michaudtime/lumary-zigbee/docs/research/stock-board-cn1-harness.jpg

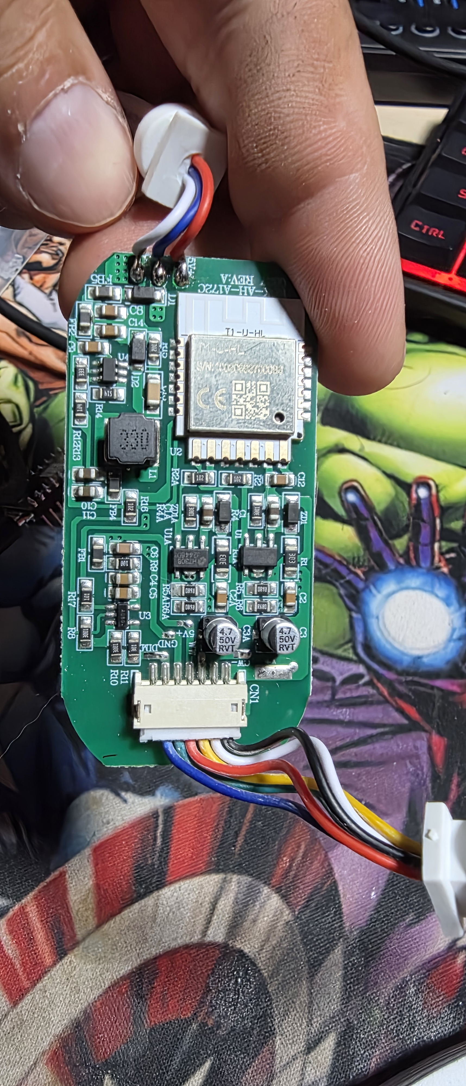
docs/research/stock-board-cn1-harness.jpg
