michaudtime/lumary-zigbee/docs/research/stock-board-cn1-labels.jpg

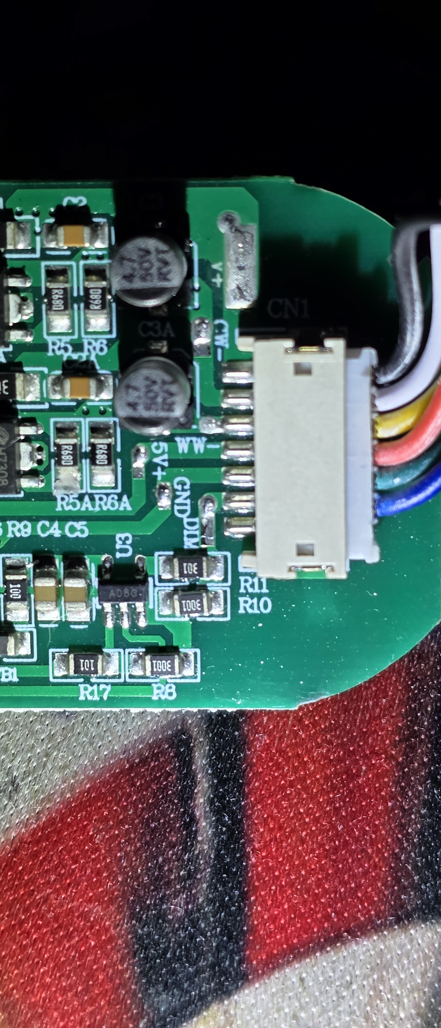
docs/research/stock-board-cn1-labels.jpg
