michaudtime/lumary-zigbee/docs/research/stock-board-top.jpg

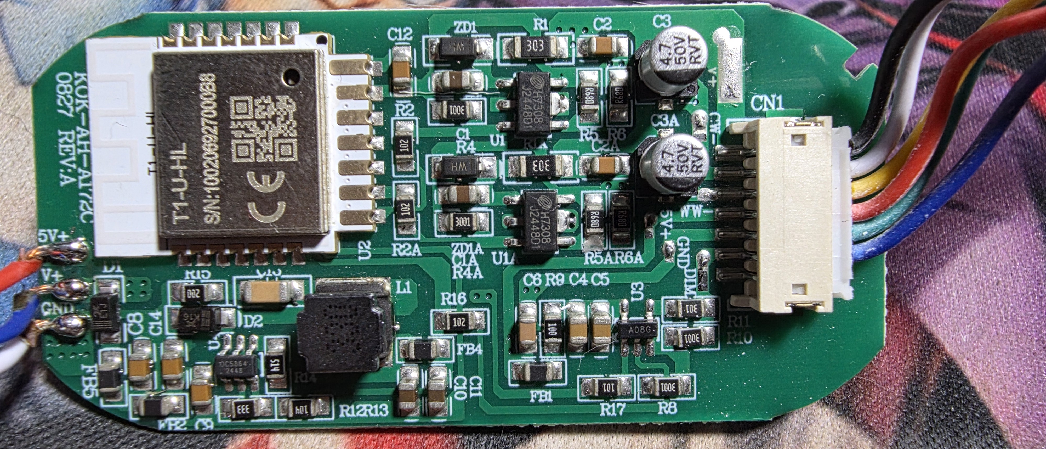
docs/research/stock-board-top.jpg
