michaudtime/lumary-zigbee/hardware/kicad/board-rounded.png

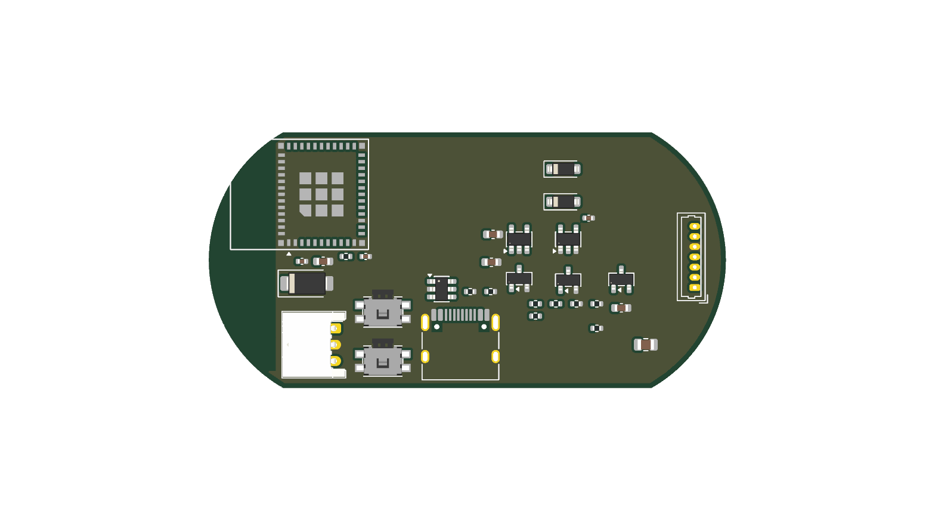
hardware/kicad/board-rounded.png
