michaudtime/lumary-zigbee/src/zigbee_light.cpp

#include "zigbee_light.h"
#include "config.h"
#include "scene_store.h"
#include "effect_params.h"
#include "identify.h"
#include "ring_command.h"
#include <Arduino.h>
#include <string.h>
#include "Zigbee.h"
#include "esp_attr.h"
#include "esp_system.h"
#include "ota_watch.h"
#include "ota_snapshot.h"

static FixtureState s_state;

// Written on the Zigbee task, read on the Arduino render task. A single
// aligned 32-bit word needs no mutex, but the volatile is load-bearing.
static volatile uint32_t s_identify_until = 0;

// OTA abort recovery -- see ota_watch.h and ota_snapshot.h.
//
// __NOINIT_ATTR: not zeroed at startup, so the record survives esp_restart()
// (and holds garbage after a power loss, which ota_snapshot_valid() rejects).
// Not RTC_NOINIT_ATTR, which esp_attr.h defines to nothing on targets without
// RTC memory.
static __NOINIT_ATTR OtaSnapshot s_ota_snapshot;
static uint16_t s_prior_recoveries = 0;   // from a restored record, else 0
static OtaWatch s_ota_watch;

// A recovery restart deferred by the backoff (see ota_recover_delay_ms() in
// ota_watch.h and item B): set when ota_watch_step() fires but the delay for
// this recovery number is non-zero, consumed once the delay has elapsed.
static bool             s_recover_pending  = false;
static OtaRecoverReason s_recover_reason;
static uint32_t         s_recover_offset;
static uint32_t         s_recover_since_ms;
static uint32_t         s_recover_delay_ms;

static bool s_restored = false;              // this boot restored an OTA snapshot
// Set and cleared on the Arduino loop task, around the library re-sync below,
// so our light callbacks ignore the library echoing back values we just gave
// it. Read by those callbacks both there (the setters' synchronous echo, same
// task) and on the Zigbee task (a real incoming command) -- which is why this
// is volatile. A command landing in that millisecond window is dropped.
static volatile bool s_suppress_light_callbacks = false;

static void apply_effect(uint8_t index);
static void publish_effect_attr();

// Shared plumbing for both light endpoints. The Arduino wrapper has no
// cluster-building API, so this reaches _cluster_list (protected on ZigbeeEP)
// and uses the raw esp_zb calls -- the same pattern the base class itself uses.
class LumaryEndpoint : public ZigbeeColorDimmableLight {
public:
    explicit LumaryEndpoint(uint8_t endpoint) : ZigbeeColorDimmableLight(endpoint) {}

    // Push this endpoint's true state to the coordinator. Nothing else does
    // this after a reboot, so Z2M keeps showing whatever it last saw --
    // typically "on" for a light that came back off.
    //
    // Deliberately not built on setLightState()/setLightLevel(): those no-op
    // when the value is unchanged (so at boot, where off == off, they would
    // push nothing at all), and when the value HAS changed they re-enter our
    // own light-changed callback, which would drag the light into MODE_COLOR.
    void publishState(bool on, uint8_t level) {
        uint8_t on_val = on ? 1 : 0;
        setAttr(ESP_ZB_ZCL_CLUSTER_ID_ON_OFF,
                ESP_ZB_ZCL_ATTR_ON_OFF_ON_OFF_ID, &on_val);
        setAttr(ESP_ZB_ZCL_CLUSTER_ID_LEVEL_CONTROL,
                ESP_ZB_ZCL_ATTR_LEVEL_CONTROL_CURRENT_LEVEL_ID, &level);
        reportAttr(ESP_ZB_ZCL_CLUSTER_ID_ON_OFF,
                   ESP_ZB_ZCL_ATTR_ON_OFF_ON_OFF_ID);
        reportAttr(ESP_ZB_ZCL_CLUSTER_ID_LEVEL_CONTROL,
                   ESP_ZB_ZCL_ATTR_LEVEL_CONTROL_CURRENT_LEVEL_ID);
    }

protected:
    // ZCL character strings are length-prefixed, not null-terminated: byte 0 is
    // the length. Same encoding the base class does by hand for manufacturer
    // and model. Without these two attributes HA's device page reads
    // "Firmware: unknown" and the update card shows a bare integer.
    void addBasicStringAttr(uint16_t attr_id, const char* value) {
        char zcl[ZB_MAX_NAME_LENGTH + 2];
        const size_t len = strlen(value);
        if (len > ZB_MAX_NAME_LENGTH) {
            log_e("Basic attr 0x%04x too long (%u)", attr_id, unsigned(len));
            return;
        }
        zcl[0] = char(len);
        memcpy(zcl + 1, value, len);
        zcl[len + 1] = '\0';

        esp_zb_attribute_list_t* basic = esp_zb_cluster_list_get_cluster(
            _cluster_list, ESP_ZB_ZCL_CLUSTER_ID_BASIC, ESP_ZB_ZCL_CLUSTER_SERVER_ROLE);
        if (basic == nullptr) {
            log_e("No basic cluster for attr 0x%04x", attr_id);
            return;
        }
        const esp_err_t ret = esp_zb_basic_cluster_add_attr(basic, attr_id, (void*)zcl);
        if (ret != ESP_OK) {
            log_e("Failed to add basic attr 0x%04x: %s", attr_id, esp_err_to_name(ret));
        }
    }

    void setAttr(uint16_t cluster, uint16_t attr, void* value) {
        esp_zb_zcl_set_attribute_val(_endpoint, cluster,
                                     ESP_ZB_ZCL_CLUSTER_SERVER_ROLE,
                                     attr, value, false);
    }

    void reportAttr(uint16_t cluster, uint16_t attr) {
        // Addressed at the coordinator explicitly rather than left to the
        // binding table (ESP_ZB_APS_ADDR_MODE_DST_ADDR_ENDP_NOT_PRESENT, which
        // is what the library's sensor endpoints use). This device was
        // interviewed by Z2M under a generic definition before the external
        // converter existed, so the bindings a sensor would rely on may never
        // have been configured -- and a report sent into an empty binding table
        // is dropped silently, which is exactly what was happening.
        esp_zb_zcl_report_attr_cmd_t cmd = {};
        cmd.zcl_basic_cmd.src_endpoint          = _endpoint;
        cmd.zcl_basic_cmd.dst_endpoint          = 1;        // coordinator
        cmd.zcl_basic_cmd.dst_addr_u.addr_short = 0x0000;   // coordinator
        cmd.address_mode     = ESP_ZB_APS_ADDR_MODE_16_ENDP_PRESENT;
        cmd.clusterID        = cluster;
        cmd.attributeID      = attr;
        cmd.direction        = ESP_ZB_ZCL_CMD_DIRECTION_TO_CLI;
        cmd.manuf_specific   = 0x00U;
        cmd.dis_default_resp = 0x00U;
        cmd.manuf_code       = 0x0000U;
        reportClusterAttribute(&cmd);
    }
};

// Endpoint 1: the inner CW/WW white string. Carries the device-level furniture
// -- Basic strings and the OTA client -- because it is endpoint 1.
class LumaryDownlight : public LumaryEndpoint {
public:
    explicit LumaryDownlight(uint8_t endpoint) : LumaryEndpoint(endpoint) {
        addBasicStringAttr(ESP_ZB_ZCL_ATTR_BASIC_SW_BUILD_ID, FW_VERSION_STRING);
        addBasicStringAttr(ESP_ZB_ZCL_ATTR_BASIC_DATE_CODE_ID, FW_DATE_CODE);
    }
};

// Endpoint 2: the outer RGB ring, plus the manufacturer-specific cluster
// carrying the effect index.
//
// The attribute is READ-ONLY on purpose. Selection comes in as a command
// instead, because zbAttributeSet is private in the base class: a subclass may
// override it but cannot call it, so intercepting attribute writes would strand
// on/off, level and colour with no handler at all.
class LumaryRing : public LumaryEndpoint {
public:
    explicit LumaryRing(uint8_t endpoint) : LumaryEndpoint(endpoint) {
        uint8_t effect = 0;
        esp_zb_attribute_list_t* custom = esp_zb_zcl_attr_list_create(LUMARY_CLUSTER_ID);
        esp_zb_custom_cluster_add_custom_attr(custom, LUMARY_ATTR_EFFECT,
                                              ESP_ZB_ZCL_ATTR_TYPE_U8,
                                              ESP_ZB_ZCL_ATTR_ACCESS_READ_ONLY,
                                              &effect);
        esp_zb_cluster_list_add_custom_cluster(_cluster_list, custom,
                                               ESP_ZB_ZCL_CLUSTER_SERVER_ROLE);
    }

    // publishState(bool, uint8_t) is inherited unchanged; this overload adds
    // the effect attribute. Non-virtual overload resolution means the base
    // two-argument version would otherwise be hidden here -- see item 7.
    using LumaryEndpoint::publishState;

    void publishState(bool on, uint8_t level, uint8_t effect) {
        LumaryEndpoint::publishState(on, level);
        setAttr(LUMARY_CLUSTER_ID, LUMARY_ATTR_EFFECT, &effect);
        // The effect attribute is deliberately NOT reported. esp_zb rejects it
        // with ESP_ERR_NOT_SUPPORTED unless the attribute carries
        // ESP_ZB_ZCL_ATTR_ACCESS_REPORTING -- and adding that flag to a custom
        // cluster attribute makes Zigbee.begin() hang before it ever starts the
        // stack (bisected on hardware 2026-08-15). The value is still written
        // above, so a READ returns the truth, which is what the Z2M converter's
        // convertGet uses.
    }
};

static LumaryDownlight s_down(DOWNLIGHT_ENDPOINT);
static LumaryRing      s_ring(RING_ENDPOINT);

// The ring endpoint reports state, level and colour together on every change,
// so a plain dim arrives carrying a colour nobody asked for. ring_command.h
// tells the two apart -- by the state/level change the library only ever
// attaches to an On/Off or Level write, never to a colour one. Its header
// carries the full reasoning, including why comparing colours cannot work.
static RingSync s_ring_sync;

// ── endpoint 1: the downlight ─────────────────────────────────────────────
// Colour-temperature capability only, so this is the only light-change
// callback it needs. No RGB callback, and no rgb_to_cct fallback: the
// coordinator can only express this endpoint's colour as mireds.
static void on_downlight_change_temp(bool state, uint8_t level, uint16_t mireds) {
    if (s_suppress_light_callbacks) return;
    s_state.down.on    = state;
    s_state.down.level = level;
    downlight_set_cct(&s_state.down, mireds);
}

// The library dispatches On/Off and Level writes through whichever colour-mode
// callback is currently active (ZigbeeColorDimmableLight::lightChangedByMode()),
// and the constructor defaults that mode to CURRENT_X_Y -- setLightColorCapabilities()
// never touches it, and this endpoint only ever advertises COLOR_TEMP, so nothing
// else flips it either. Without these two shims, on/off and level land on the
// null RGB callback and get dropped silently until some colour-temperature
// command switches the mode to TEMPERATURE -- which on endpoint 1 means the
// wall switch does nothing after every power cycle, until someone touches the
// CCT slider in Home Assistant. Both shims ignore the colour arguments: this
// endpoint has no colour dice, so there is nothing there to act on.
static void on_downlight_change_rgb(bool state, uint8_t /*r*/, uint8_t /*g*/, uint8_t /*b*/, uint8_t level) {
    if (s_suppress_light_callbacks) return;
    s_state.down.on    = state;
    s_state.down.level = level;
}

// HSV callback carries (state, hue, saturation, value) -- no separate level
// parameter; `value` doubles as the brightness/level component (see
// ZigbeeColorDimmableLight.h). This mode is unreachable in practice, since the
// downlight never advertises HUE_SATURATION, but it costs nothing to cover.
static void on_downlight_change_hsv(bool state, uint8_t /*hue*/, uint8_t /*sat*/, uint8_t value) {
    if (s_suppress_light_callbacks) return;
    s_state.down.on    = state;
    s_state.down.level = value;
}

// ── endpoint 2: the ring ──────────────────────────────────────────────────
static void on_ring_change_rgb(bool state, uint8_t r, uint8_t g, uint8_t b, uint8_t level) {
    if (s_suppress_light_callbacks) return;
    // Returns true only when the ring left scene mode, so stop naming an effect.
    if (ring_apply_rgb(&s_state.ring, &s_ring_sync, state, CRGB{r, g, b}, level)) {
        publish_effect_attr();
    }
}

// The ring advertises HUE_SATURATION as well as X_Y, so a scene recall, group
// command, or a different coordinator can latch the colour mode to
// HUE_SATURATION -- after which every On/Off and Level command would be
// dropped the same way the downlight's were (item 1) unless this is
// registered. RingState already stores hue/sat directly, so this sets them
// without round-tripping through RGB the way on_ring_change_rgb has to.
//
// Note this path is reachable for a NON-colour command too: a coordinator can
// write the ColorMode attribute directly, latching the library into HSV with
// its hue/sat still at the power-up default and no callback of its own -- after
// which the next On/Off dispatches through here carrying hue 0 / sat 0.
static void on_ring_change_hsv(bool state, uint8_t hue, uint8_t sat, uint8_t value) {
    if (s_suppress_light_callbacks) return;
    if (ring_apply_hsv(&s_state.ring, &s_ring_sync, state, hue, sat, value)) {
        publish_effect_attr();
    }
}

// Identify is an overlay: it does not touch FixtureState, so when the deadline
// passes the fixture resumes whatever it was doing with no restore step.
//
// ZCL treats IdentifyTime = 0 as "stop identifying", which is how a
// coordinator cancels. Encoding it as a deadline of now makes
// identify_active() false immediately, rather than scheduling a zero-length
// blink that would leave the ring lit for one frame.
static void on_identify(uint16_t time) {
    const uint32_t now = millis();
    s_identify_until = (time == 0) ? now : now + uint32_t(time) * 1000;
    log_i("Zigbee identify for %us", time);
}

// Effect selection. Runs on the Zigbee task. Everything is validated before it
// reaches light_state, because this payload comes straight off the air.
static void on_custom_command(const esp_zb_zcl_custom_cluster_command_message_t* message) {
    if (message->info.cluster != LUMARY_CLUSTER_ID) return;
    if (message->info.command.id != LUMARY_CMD_SET_EFFECT) {
        log_w("Ignored unknown Lumary command 0x%02x", message->info.command.id);
        return;
    }
    if (message->data.value == nullptr || message->data.size < 1) {
        log_w("Ignored empty set-effect command");
        return;
    }
    apply_effect(*(uint8_t*)message->data.value);
}

// Reads the OTA client cluster's ImageUpgradeStatus and FileOffset from
// endpoint 1, where addOTAClient() put the client. Called on the Arduino loop
// task, so the stack lock is required. Returns false (skip this sample) if the
// lock is busy or either attribute is missing.
static bool read_ota_client(uint8_t* status, uint32_t* offset) {
    if (!esp_zb_lock_acquire(pdMS_TO_TICKS(50))) return false;
    esp_zb_zcl_attr_t* st = esp_zb_zcl_get_attribute(DOWNLIGHT_ENDPOINT,
        ESP_ZB_ZCL_CLUSTER_ID_OTA_UPGRADE, ESP_ZB_ZCL_CLUSTER_CLIENT_ROLE,
        ESP_ZB_ZCL_ATTR_OTA_UPGRADE_IMAGE_STATUS_ID);
    esp_zb_zcl_attr_t* off = esp_zb_zcl_get_attribute(DOWNLIGHT_ENDPOINT,
        ESP_ZB_ZCL_CLUSTER_ID_OTA_UPGRADE, ESP_ZB_ZCL_CLUSTER_CLIENT_ROLE,
        ESP_ZB_ZCL_ATTR_OTA_UPGRADE_FILE_OFFSET_ID);
    const bool ok = st && off && st->data_p && off->data_p;
    if (ok) {
        *status = *(uint8_t*)st->data_p;
        *offset = *(uint32_t*)off->data_p;
    }
    esp_zb_lock_release();
    return ok;
}

// A failed download leaves the Arduino library's OTA parser mid-image (it only
// resets on success), so every retry would fail INVALID_IMAGE until a restart.
// Snapshot the light, restart, and let zigbee_light_init() put it back; the
// next image query then retries a scheduled update from scratch.
static void ota_recover(OtaRecoverReason reason, uint32_t offset) {
    ota_snapshot_save(&s_ota_snapshot, &s_state, reason, offset, s_prior_recoveries);
    log_w("OTA %s at offset %lu -- recovery #%u, restarting",
          reason == OTA_RECOVER_STALL ? "stalled" : "aborted",
          (unsigned long)offset, s_ota_snapshot.recoveries);
    delay(100);   // let the log line out
    esp_restart();
}

void zigbee_light_init() {
    fixture_state_init(&s_state);
    ring_sync_init(&s_ring_sync);
    s_state.ring.scene = scene_store_get_active();

    // After an OTA recovery restart, put the light back as it was -- see
    // ota_recover(). Only a software restart with a valid record qualifies; a
    // power loss leaves garbage the checksum rejects. Invalidated on every boot
    // either way, so a record can restore at most once.
    if (esp_reset_reason() == ESP_RST_SW && ota_snapshot_valid(&s_ota_snapshot)) {
        s_state            = s_ota_snapshot.state;
        s_prior_recoveries = s_ota_snapshot.recoveries;
        s_restored         = true;
        log_w("Restored light state after OTA recovery #%u (%s at offset %lu)",
              s_ota_snapshot.recoveries,
              s_ota_snapshot.reason == OTA_RECOVER_STALL ? "stall" : "abort",
              (unsigned long)s_ota_snapshot.offset);
        // No colour-sentinel seeding needed here any more: ring_command.h tells
        // a colour command from an On/Off or Level one without consulting the
        // colour at all, so the library sitting at its power-up default costs
        // nothing. The state/level baseline is still seeded to the library's
        // defaults above and moved to the restored values by the re-sync in
        // zigbee_light_loop(), once Zigbee.begin() has actually joined.
    }
    ota_snapshot_invalidate(&s_ota_snapshot);
    ota_watch_init(&s_ota_watch);

    // ── endpoint 1: downlight ──
    s_down.onLightChangeTemp(on_downlight_change_temp);
    // Mode-agnostic shims so On/Off and Level are never dropped -- see the
    // comment above on_downlight_change_rgb (item 1).
    s_down.onLightChangeRgb(on_downlight_change_rgb);
    s_down.onLightChangeHsv(on_downlight_change_hsv);
    s_down.onIdentify(on_identify);
    s_down.setManufacturerAndModel("Lumary", "LumaryBrainRevA");
    // Mains-powered ceiling fixture, not battery -- left at the default
    // (setPowerSource never called) the Basic cluster's power source attribute
    // stays 0x00 Unknown, which is what Z2M's device page was showing next to
    // the (correct) Router type.
    s_down.setPowerSource(ZB_POWER_SOURCE_MAINS);
    s_down.setLightColorCapabilities(ZIGBEE_COLOR_CAPABILITY_COLOR_TEMP);
    if (!s_down.setLightColorTemperatureRange(CCT_MIRED_COOL, CCT_MIRED_WARM)) {
        log_e("Failed to publish colour temperature range");
    }

    // Zigbee OTA, on endpoint 1 only -- one client per device. The coordinator
    // only offers images numbered above the running version, so ZB_FW_VERSION
    // must match the .ota image's --file-version.
    if (!s_down.addOTAClient(ZB_FW_VERSION, ZB_FW_VERSION_DL, ZB_HW_VERSION,
                             ZB_MANUFACTURER_CODE, ZB_IMAGE_TYPE)) {
        log_e("Failed to add OTA client");
    }

    // ── endpoint 2: accent ring ──
    // No colour temperature: the ring has no white die, and advertising CCT
    // would put a control in Home Assistant that lies.
    s_ring.onLightChangeRgb(on_ring_change_rgb);
    s_ring.onLightChangeHsv(on_ring_change_hsv);
    s_ring.onCustomClusterCommand(on_custom_command);
    s_ring.setManufacturerAndModel("Lumary", "LumaryBrainRevA");
    s_ring.setPowerSource(ZB_POWER_SOURCE_MAINS);
    s_ring.setLightColorCapabilities(ZIGBEE_COLOR_CAPABILITY_HUE_SATURATION
                                   | ZIGBEE_COLOR_CAPABILITY_X_Y);

    Zigbee.addEndpoint(&s_down);
    Zigbee.addEndpoint(&s_ring);

    // Router, not end device: these are mains-powered ceiling fixtures, so each
    // one should extend the mesh for the others.
    if (!Zigbee.begin(ZIGBEE_ROUTER)) {
        // Deliberately not fatal. A light that can't reach the network must
        // still turn on locally, so carry on rendering and let the caller retry.
        log_e("Zigbee failed to start; continuing with local control only");
        return;
    }
    log_i("Zigbee started, waiting for network");
}

bool zigbee_light_connected() {
    return Zigbee.connected();
}

void zigbee_light_loop() {
    // OTA abort/stall watch -- see ota_watch.h.
    static uint32_t s_ota_sample_at = 0;
    const uint32_t now = millis();
    if (Zigbee.connected() && now - s_ota_sample_at >= OTA_WATCH_SAMPLE_MS) {
        s_ota_sample_at = now;
        uint8_t  status;
        uint32_t offset;
        if (read_ota_client(&status, &offset)) {
            const OtaRecoverReason r = ota_watch_step(&s_ota_watch, status, offset, now);
            if (r != OTA_RECOVER_NONE) {
                const uint16_t n     = uint16_t(s_prior_recoveries + 1);
                const uint32_t delay = ota_recover_delay_ms(n);
                if (delay == 0) {
                    ota_recover(r, ota_watch_progress(&s_ota_watch));
                } else {
                    log_w("OTA %s at offset %lu -- recovery #%u deferred %lu s (backoff)",
                          r == OTA_RECOVER_STALL ? "stalled" : "aborted",
                          (unsigned long)ota_watch_progress(&s_ota_watch), n,
                          (unsigned long)(delay / 1000));
                    s_recover_pending  = true;
                    s_recover_reason   = r;
                    s_recover_offset   = ota_watch_progress(&s_ota_watch);
                    s_recover_since_ms = now;
                    s_recover_delay_ms = delay;
                }
            }
        }
    }

    // A deferred recovery restart -- see item B. Deliberately not gated on
    // Zigbee.connected(): the watcher has already fired for this boot and
    // won't again, so this is the only path left that still needs to run
    // while we wait out the backoff.
    if (s_recover_pending && now - s_recover_since_ms >= s_recover_delay_ms) {
        s_recover_pending = false;
        ota_recover(s_recover_reason, s_recover_offset);
    }

    // The OTA query can only be issued once we're on a network. After this first
    // request the stack re-queries hourly on its own.
    static bool s_joined_once = false;
    if (!s_joined_once && Zigbee.connected()) {
        s_joined_once = true;
        s_down.requestOTAUpdate();
        log_i("Zigbee joined; OTA update requested");

        // A restored fixture must bring the light library's private on/off and
        // level copies into line, or an Off to a restored-on light is swallowed
        // (zbAttributeSet only calls back on a change). Normal boots skip this.
        if (s_restored) {
            s_suppress_light_callbacks = true;
            s_down.setLightLevel(s_state.down.level);
            s_down.setLightState(s_state.down.on);
            s_ring.setLightLevel(s_state.ring.level);
            s_ring.setLightState(s_state.ring.on);
            s_suppress_light_callbacks = false;
            // The library moved but never called back, so move the ring's
            // baseline with it. Left at the boot defaults, a genuine colour
            // command that happened to match them would read as an On/Off and
            // be dropped instead of applied.
            ring_sync_note(&s_ring_sync, s_state.ring.on, s_state.ring.level);
        }

        // Tell the coordinator what we actually are, before anything asks. The
        // light boots off with the stored effect, and the effect attribute is
        // built during static init -- before setup() opens NVS -- so without
        // this both are wrong: HA shows the pre-reboot on/off state, and a read
        // reports effect 0 whatever is really running.
        const uint8_t effect = ring_effect_value(&s_state.ring);
        s_down.publishState(s_state.down.on, s_state.down.level);
        s_ring.publishState(s_state.ring.on, s_state.ring.level, effect);
        log_i("Published state: downlight on=%d level=%u / ring on=%d level=%u effect=%u",
              s_state.down.on, s_state.down.level,
              s_state.ring.on, s_state.ring.level, effect);
    }
}

const FixtureState* zigbee_light_state() {
    return &s_state;
}

// Mirrors the running effect into the attribute so a read -- which is all the
// coordinator can do, the attribute being unreportable -- returns the truth.
// Called on transitions OUT of effect mode as well as into one: without that
// half the attribute goes on naming the last effect while the ring holds a
// static colour, and Home Assistant's dropdown shows an effect that stopped.
static void publish_effect_attr() {
    uint8_t value = ring_effect_value(&s_state.ring);
    esp_zb_zcl_set_attribute_val(RING_ENDPOINT, LUMARY_CLUSTER_ID,
                                 ESP_ZB_ZCL_CLUSTER_SERVER_ROLE,
                                 LUMARY_ATTR_EFFECT, &value, false);
}

// Runs on the Zigbee task. ring_set_scene rejects an out-of-range index
// outright, so re-read the state rather than trusting what was asked for --
// otherwise a bad write would persist a scene the effect engine can't render.
static void apply_effect(uint8_t index) {
    if (index == LIGHT_EFFECT_NONE) {
        // "None" in the Home Assistant dropdown: stop the effect and hold the
        // colour already on show. Deliberately NOT persisted -- the stored
        // active scene is what a power cycle should come back to.
        ring_clear_scene(&s_state.ring);
        publish_effect_attr();
        log_i("Effect cleared; holding the current colour");
        return;
    }

    ring_set_scene(&s_state.ring, index, EFFECT_COUNT);
    if (s_state.ring.scene != index) {
        log_w("Ignored out-of-range effect %u", index);
        return;
    }
    scene_store_set_active(s_state.ring.scene);
    publish_effect_attr();
    zigbee_light_report();
    log_i("Effect %u selected", s_state.ring.scene);
}

void zigbee_light_set_effect(uint8_t index) {
    apply_effect(index);
}

void zigbee_light_report() {
    s_ring.setLightState(s_state.ring.on);
    s_ring.setLightLevel(s_state.ring.level);
}

uint32_t zigbee_light_identify_until() {
    return s_identify_until;
}
