michaudtime/lumary-zigbee/src/zigbee_light.h

#pragma once
#include "light_state.h"

// Thin adapter between the Arduino Zigbee stack and light_state. Everything
// with real decision-making lives in light_state.h (which is host-tested);
// this file only wires the callbacks up and owns the endpoint.

// Brings up the Zigbee stack and the light endpoint. Non-blocking: the light
// renders locally whether or not a network is ever joined.
void zigbee_light_init();

// True once joined to a network.
bool zigbee_light_connected();

// Call every loop(). Handles work that can only happen after joining, such as
// the first OTA query.
void zigbee_light_loop();

// Live state, updated from Zigbee callbacks. One object, two independent
// halves -- see FixtureState in light_state.h.
const FixtureState* zigbee_light_state();

// Selects one of the six ring effects and persists it to NVS. Normally driven
// from the coordinator sending LUMARY_CMD_SET_EFFECT on RING_ENDPOINT; exposed
// for a future local button. Out-of-range indices are ignored, not clamped.
//
// LIGHT_EFFECT_NONE stops the effect and holds the colour already on show,
// which is what "none" in Home Assistant's effect dropdown sends. It is not
// persisted -- a power cycle returns to the stored effect.
//
// Stepping (the switch's double-tap) deliberately lives in the hub automation,
// which reads the current effect and writes (n +/- 1) mod EFFECT_COUNT. There is
// no next/prev here because the Inovelli's multi-tap events go to the
// coordinator rather than to a bound light, so a hub is in the loop regardless.
void zigbee_light_set_effect(uint8_t index);

// Mirrors the current state back to the coordinator after a local change, so
// Home Assistant / Z2M don't show stale values.
void zigbee_light_report();

// Deadline (millis) until which the fixture should render the Identify blink.
// The render loop compares it with identify_active(); a value equal to or
// behind now means "not identifying".
uint32_t zigbee_light_identify_until();
